jeremiahrose/SparkFun_Thing_Plus_ESP32-S3/Documents/microSD.png

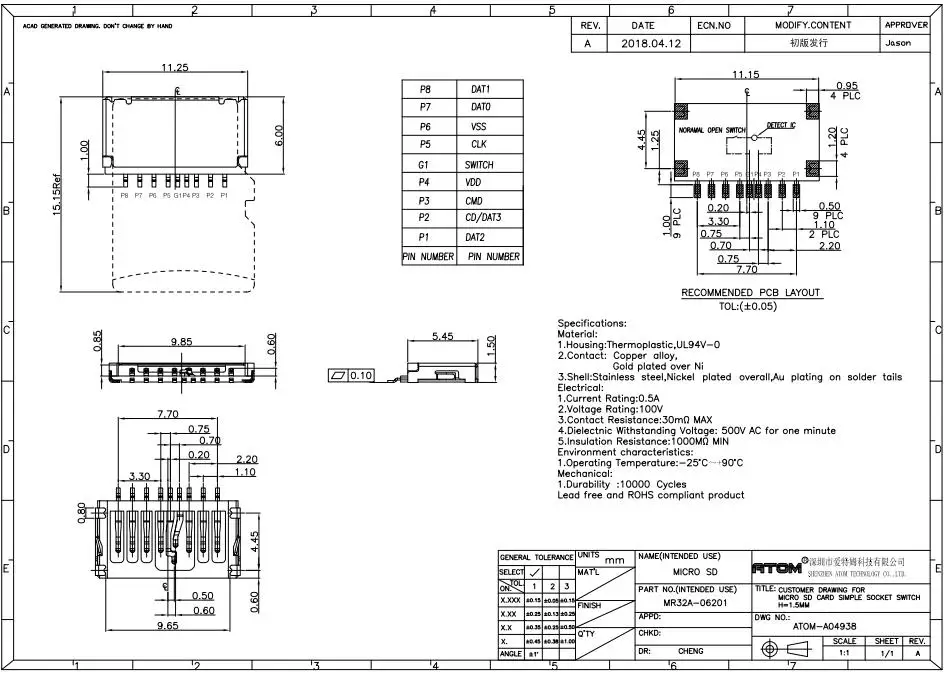
Documents/microSD.png
